visakhanc/usbXR/bootloader/remote-bootloader-mega8/schematic.sch

## EAGLE design bootloader/remote-bootloader-mega8/schematic.sch (2017-11-20, last stored version)

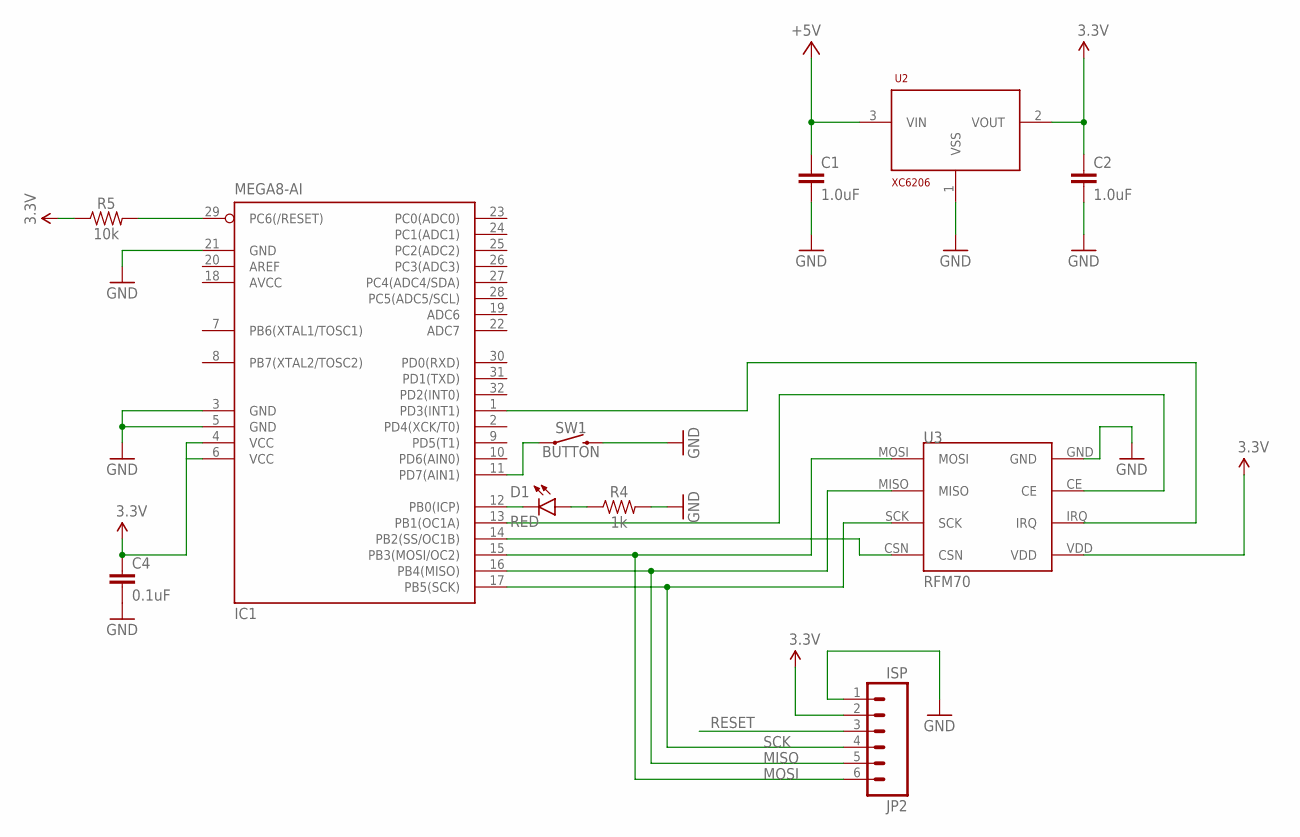
[picture p8: schematic schematic.sch]

Parts:
C1, C2: 1.0uF; 0603
C4: 0.1uF; 0603
D1: RED; LED-1206
IC1: MEGA8-AI; TQFP32-08
JP2: ISP; 1X06-SMD_EDGE
R4: 1k; 0603
R5: 10k; 0603
SW1: BUTTON; TACTILE_SWITCH_3X4MM
U2: XC6206; SOT23-3
U3: RFM70; RFM70_SMD

Connections:
3.3V: C2.1, C4.1, IC1.4 (VCC), IC1.6 (VCC), JP2.2, R5.1, U2.2 (VOUT), U3.VDD
+5V: C1.1, U2.3 (VIN)
CE: IC1.13 (PB1(OC1A)), U3.CE
CSN: IC1.14 (PB2(SS/OC1B)), U3.CSN
GND: C1.2, C2.2, C4.2, IC1.21 (GND), JP2.1, R4.2, SW1.2, U2.1 (VSS), U3.GND
IRQ: IC1.1 (PD3(INT1)), U3.IRQ
MISO: IC1.16 (PB4(MISO)), JP2.5, U3.MISO
MOSI: IC1.15 (PB3(MOSI/OC2)), JP2.6, U3.MOSI
unnamed: IC1.29 (PC6(/RESET)), R5.2
unnamed: D1.C, IC1.12 (PB0(ICP))
unnamed: IC1.11 (PD7(AIN1)), SW1.1
unnamed: D1.A, R4.1
RESET: JP2.3
SCK: IC1.17 (PB5(SCK)), JP2.4, U3.SCK
